eleqian/WiDSO/MCU/BootLoader/udisk/mass_mal.c

/*
 * 存储器驱动模块 for stm32f103c8 & stm32l151c8
 * eleqian 2014-10-23
 */

#include "hw_config.h"
#include "mass_mal.h"
#include "string.h"
#ifdef MAL_SPI_FLASH
#include "spi_flash.h"
#endif // MAL_SPI_FLASH

// 设备信息
uint32_t Mass_Block_Size[MAX_LUN];      // 块大小
uint32_t Mass_Block_Count[MAX_LUN];     // 块数目
uint32_t Mass_Memory_Size[MAX_LUN];     // 空间大小

#ifdef MCU_STM32F103C8
// 内部Flash磁盘文件系统空间
// 基于RAM可以避免使用Flash，同时保证每次更新bin都在固定位置
// 空间分配：1k引导扇区(只使用前512Byte) + 1k FAT表+ 1k根目录
static uint8_t Mass_FAT[1024 * 3];

// 内部Flash磁盘的启动扇区
// 磁盘参数：扇区大小1k，1个引导扇区，1个FAT表，1个根目录扇区
// 总大小115k，可用空间115-3=112k
const unsigned char Mass_BootSector[512] = {
	0xEB, 0x3C, 0x90, 0x4D, 0x53, 0x44, 0x4F, 0x53, 0x35, 0x2E, 0x30, 0x00, 0x04, 0x01, 0x01, 0x00, 
	0x01, 0x20, 0x00, 0x73, 0x00, 0xF8, 0x01, 0x00, 0x01, 0x00, 0x01, 0x00, 0x00, 0x00, 0x00, 0x00, 
	0x00, 0x00, 0x00, 0x00, 0x80, 0x00, 0x29, 0x0D, 0x89, 0xE0, 0x04, 0x55, 0x53, 0x42, 0x5F, 0x42, 
	0x4C, 0x00, 0x20, 0x20, 0x20, 0x20, 0x46, 0x41, 0x54, 0x31, 0x36, 0x00, 0x20, 0x20, 0x33, 0xC9, 
	0x8E, 0xD1, 0xBC, 0xF0, 0x7B, 0x8E, 0xD9, 0xB8, 0x00, 0x20, 0x8E, 0xC0, 0xFC, 0xBD, 0x00, 0x7C, 
	0x38, 0x4E, 0x24, 0x7D, 0x24, 0x8B, 0xC1, 0x99, 0xE8, 0x3C, 0x01, 0x72, 0x1C, 0x83, 0xEB, 0x3A, 
	0x66, 0xA1, 0x1C, 0x7C, 0x26, 0x66, 0x3B, 0x07, 0x26, 0x8A, 0x57, 0xFC, 0x75, 0x06, 0x80, 0xCA, 
	0x02, 0x88, 0x56, 0x02, 0x80, 0xC3, 0x10, 0x73, 0xEB, 0x33, 0xC9, 0x8A, 0x46, 0x10, 0x98, 0xF7, 
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

    if (DataLength & 0x3) { // Not an aligned data
        /*for (idx = DataLength; idx < ((DataLength & 0xFFFC) + 4); idx++) {
            MAL_Buffer[idx] = 0xFF;
        }*/
        return MAL_FAIL;
    }

    // Initialize the intermediate buffer pointer
    mempBuffer = memBuffer;

    // If the address is not aligned to half-page fill the first location with existing data
    if (((uint32_t)memPointer & 0x7F) != 0) {
        // get the aligned address
        tmp = (uint32_t *)((uint32_t)memPointer & 0xFFFFFF80);
        // Read the first part from the memory
        while (tmp < memPointer) {
            *(uint32_t *)(mempBuffer++) = *(uint32_t *)(tmp++);
        }
    }

    while (malPointer < (uint32_t *)(Writebuff + DataLength)) {
        // Fill with the received buffer
        while (mempBuffer < (memBuffer + 32)) {
            // If there are still data available in the received buffer
            if (malPointer < ((uint32_t *)Writebuff + DataLength)) {
                *(uint32_t *)(mempBuffer++) = *(uint32_t *)(malPointer++);
            } else {
                // no more data available in the received buffer: fill remaining with dummy 0
                *(uint32_t *)(mempBuffer++) = 0;
            }
        }
        // Write the buffer to the memory
        FLASH_ProgramHalfPage(((uint32_t)memPointer & 0xFFFFFF80), (uint32_t *)(memBuffer));
        // Increment the memory pointer
        memPointer = (uint32_t *)(((uint32_t)memPointer & 0xFFFFFF80) + (32 * 4));
        // Reinitialize the intermediate buffer pointer
        mempBuffer = memBuffer;
    }
#else
    uint32_t idx = 0;

    // Data received are Word multiple
    for (idx = 0; idx <  DataLength; idx = idx + 4) {
        FLASH_FastProgramWord(WriteAddress, *(uint32_t *)(Writebuff + idx));
        WriteAddress += 4;
    }
#endif
#endif //MCU_STM32L151C8

#ifdef MCU_STM32F103C8
    uint32_t idx = 0;

    // Data received are Word multiple
    for (idx = 0; idx <  DataLength; idx = idx + 4) {
        FLASH_ProgramWord(WriteAddress, *(uint32_t *)(Writebuff + idx));
        WriteAddress += 4;
    }
#endif //MCU_STM32F103C8

    return MAL_OK;
}

// 读内部Flash
// 参数：读地址，数据缓冲区，读字节数
// 返回：MAL_OK
uint16_t FLASH_If_Read(uint32_t ReadAddress, uint8_t *Readbuff, uint32_t DataLength)
{
    uint32_t idx = 0;
    __IO uint32_t *malPointer = (uint32_t *)Readbuff;
    __IO uint32_t *memPointer = (uint32_t *)ReadAddress;

    for (idx = 0; idx < DataLength; idx += 4) {
        *malPointer++ = *memPointer++;
    }

    return MAL_OK;;
}

/*-----------------------------------*/

// MAL层初始化
// 参数：设备序号
// 返回：MAL_OK/MAL_FAIL
uint16_t MAL_Init(uint8_t lun)
{
    switch (lun) {
    case 0:
#ifdef MCU_STM32L151C8
        FLASH_Unlock();
        FLASH_ClearFlag(FLASH_FLAG_OPTVERRUSR);
        // 复制启动扇区到RAM
        memcpy(&Mass_FAT[0x0], Mass_BootSector, sizeof(Mass_BootSector));
        // 添加磁盘卷标到目录表
        memcpy(&Mass_FAT[0x400], Mass_LabelEntry, sizeof(Mass_LabelEntry));
#endif //MCU_STM32L151C8
#ifdef MCU_STM32F103C8
        FLASH_Unlock();
        FLASH_ClearFlag(FLASH_FLAG_EOP | FLASH_FLAG_PGERR | FLASH_FLAG_WRPRTERR);	
        // 复制启动扇区到RAM
        memcpy(&Mass_FAT[0x0], Mass_BootSector, sizeof(Mass_BootSector));
        // 添加磁盘卷标到目录表
        memcpy(&Mass_FAT[0x800], Mass_LabelEntry, sizeof(Mass_LabelEntry));
#endif //MCU_STM32F103C8
        break;
#ifdef MAL_SPI_FLASH
    case 1:
        SPI_Flash_Init();
        //SPI_Flash_ReadJEDECID();
        //SPI_Flash_ReadStatus();
        //SPI_Flash_ProtectionDisable();
        break;
#endif //MAL_SPI_FLASH
    default:
        return MAL_FAIL;
    }

    return MAL_OK;
}

// MAL层写数据
// 参数：设备序号，写地址，数据指针，数据大小
// 返回：MAL_OK/MAL_FAIL
uint16_t MAL_Write(uint8_t lun, uint32_t Memory_Offset, const uint8_t *Writebuff, uint16_t Transfer_Length)
{
    switch (lun) {
    case 0:
        if (Memory_Offset < sizeof(Mass_FAT)) {
            memcpy(Mass_FAT + Memory_Offset, Writebuff, Transfer_Length);
        } else {
            Memory_Offset -= sizeof(Mass_FAT);
            FLASH_If_Erase(INTER_FLASH_BASE_ADDR + Memory_Offset, Transfer_Length);
            FLASH_If_Write(INTER_FLASH_BASE_ADDR + Memory_Offset, Writebuff, Transfer_Length);
        }
        break;
#ifdef MAL_SPI_FLASH
    case 1:
        SPI_Flash_SectorErase(Memory_Offset);
        SPI_Flash_Write(Memory_Offset, Writebuff, Transfer_Length);
        break;
#endif // MAL_SPI_FLASH
    default:
        return MAL_FAIL;
    }

    return MAL_OK;
}

// MAL层读数据
// 参数：设备序号，读地址，数据缓冲区，读大小
// 返回：MAL_OK/MAL_FAIL
uint16_t MAL_Read(uint8_t lun, uint32_t Memory_Offset, uint8_t *Readbuff, uint16_t Transfer_Length)
{
    switch (lun) {
    case 0:
        if (Memory_Offset < sizeof(Mass_FAT)) {
            memcpy(Readbuff, Mass_FAT + Memory_Offset, Transfer_Length);
        } else {
            Memory_Offset -= sizeof(Mass_FAT);
            FLASH_If_Read(INTER_FLASH_BASE_ADDR + Memory_Offset, Readbuff, Transfer_Length);
        }
        break;
#ifdef MAL_SPI_FLASH
    case 1:
        SPI_Flash_Read(Memory_Offset, Readbuff, Transfer_Length);
        break;
#endif // MAL_SPI_FLASH
    default:
        return MAL_FAIL;
    }

    return MAL_OK;
}

// MAL层获取信息
// 参数：设备序号
// 返回：MAL_OK/MAL_FAIL
uint16_t MAL_GetStatus(uint8_t lun)
{
    switch (lun) {
    case 0:
#if INTER_FLASH_PAGE_SIZE == 256
        // FAT文件系统要求最小扇区大小为512
        Mass_Block_Size[0] = INTER_FLASH_PAGE_SIZE * 2;
        Mass_Block_Count[0] = INTER_FLASH_PAGE_COUNT / 2;
#else
        Mass_Block_Size[0] = INTER_FLASH_PAGE_SIZE;
        Mass_Block_Count[0] = INTER_FLASH_PAGE_COUNT;
#endif // INTER_FLASH_PAGE_SIZE
        break;
#ifdef MAL_SPI_FLASH
    case 1:
        Mass_Block_Size[1] = SPI_FLASH_SECTOR_SIZE;
        Mass_Block_Count[1] = SPI_FLASH_SECTOR_COUNT;
        break;
#endif // MAL_SPI_FLASH
    default:
        return MAL_FAIL;
    }

    Mass_Memory_Size[lun] = Mass_Block_Size[lun] * Mass_Block_Count[lun];

    return MAL_OK;
}
